listofoptions/ind-sense/layout/mini xt 9.75u lefty.png

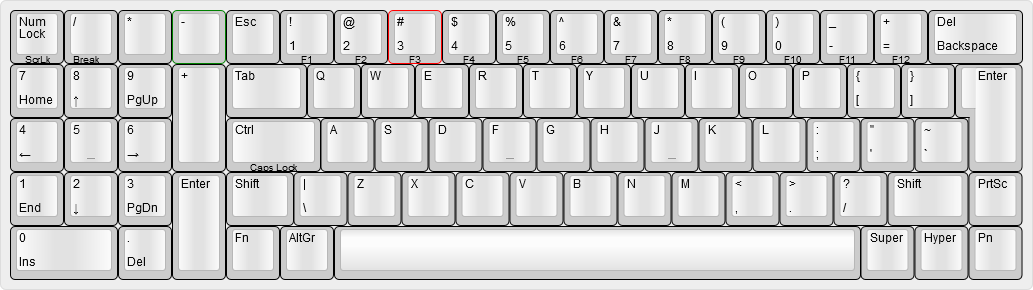
layout/mini xt 9.75u lefty.png
