listofoptions/ind-sense/spice/theory of operation.asc

L1: ind2; 1.43741567552195µ; Rser=24.6255310947963n Cpar=91.7122498180724p
L2: ind2; 3.41677831647223µ; Rser=24.6255310947963n Cpar=91.7122498180724p
R1: res; 2640
R2: res; 2640
V1: voltage; PULSE(0 3.3 0 1us 1us 48us 100us); AC 3.3
V2: voltage; PULSE(0 3.3 0 1us 1us 48us 100us); AC 3.3
Named nets: 0
;tran 0 300u 0 10000u startup
.ac dec 1000 100k 500
